harvie256/ESPTempMonitor/Photos/IMG_1801.JPG

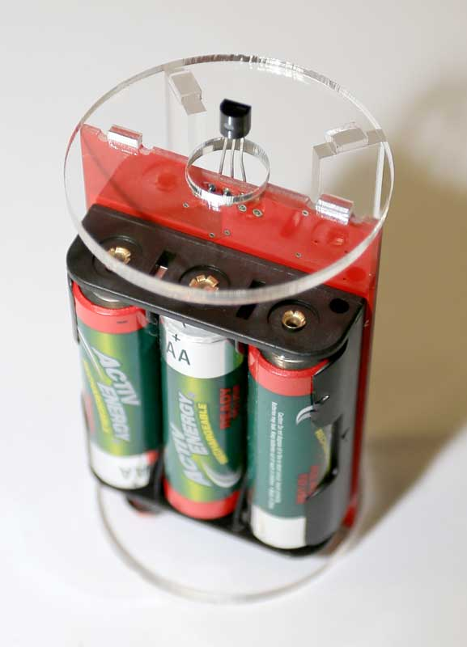
Photos/IMG_1801.JPG
